syn-ack-zack/HTH-Elite-2019-Badge/software/data/www/images/W9Vo.gif

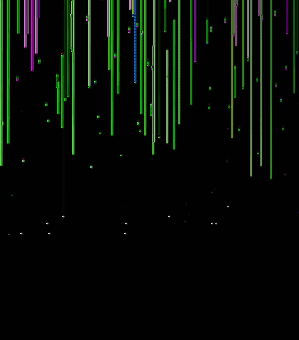
software/data/www/images/W9Vo.gif
