syn-ack-zack/HTH-Elite-2019-Badge/software/data/www/images/Yed2.gif

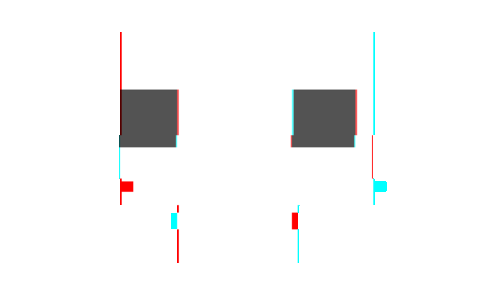
software/data/www/images/Yed2.gif
